gcdavidq/Project_FdD/FdD/Entregables/2.-Definción_del_problema.md

# 2. DEFINICIÓN DEL PROBLEMA:

### **"La cultura ambiental ineficiente respecto a la clasificación de los residuos sólidos domiciliarios en San Martín de Porres, Lima."**

HERRAMIENTAS A UTILIZAR PARA DEFINIR EL PROBLEMA
1.PREGUNTAS AL USUARIO 
Se envió un formulario a los usuarios donde contiene preguntas acerca de la organización de los residuos sólidos. Ellos podrán responder y de esa manera nos daremos cuenta qué tanto conocen acerca del tema o qué tan satisfechos se encuentran con la organización de estos residuos.

1. ¿Qué opina usted acerca de la contaminación ambiental? ¿Cree usted qué el ministerio de ambiente está realizando un buen trabajo?

2. ¿Usted separa los residuos sólidos en su hogar por orgánicos (cáscaras de verduras o frutas) e inorgánicos (papel, aluminio, vidrio etc)? En caso negativo, sí cobran alguna penalidad monetaria por no hacerlo, ¿Usted lo haría?

3. ¿Usted puede diferenciar qué residuos debe ir en cada color de tacho?
4. Si existiera una recolección separada (orgánicos e inorgánicos), ¿usted se motivaría a reciclar?  O si ya recicla, ¿lo haría con mayor gusto?

5. Si los tachos de basura tuvieran una forma relacionada a lo que se debe depositar en él ¿Cree usted que resultaría más fácil clasificar los residuos? Ejemplo: Botella gigante para reciclar plásticos.

6. Si existieran incentivos económicos en el manejo del reciclaje, el manejo de los residuos sólidos, ¿mejoraría o empeoraría? 

7. ¿Qué estrategias considera usted que deben ser usadas para que en nuestro país haya un programa de reciclaje efectivo?

**Enlace de la encuesta:** https://forms.gle/2g3sSfPMJ8BGpuau7

**Evidencias de la encuesta realizada:** https://docs.google.com/spreadsheets/d/1U6mOmiROQCDAYu15ibwH8KvVmI2ISACFjVF0aS-_oU8/edit?usp=sharing

  ***Figura 1:*** Resultados gráficos de la encuesta. Elaboración propia.

**2. MAPA DE EMPATÍA**

El mapa de empatía es una herramienta visual que ayuda a comprender las necesidades, pensamientos, emociones y comportamientos de un usuario(1). Las respuestas de Google Forms nos ayudarán para una buena organización de este mapa.

<p align= "center">
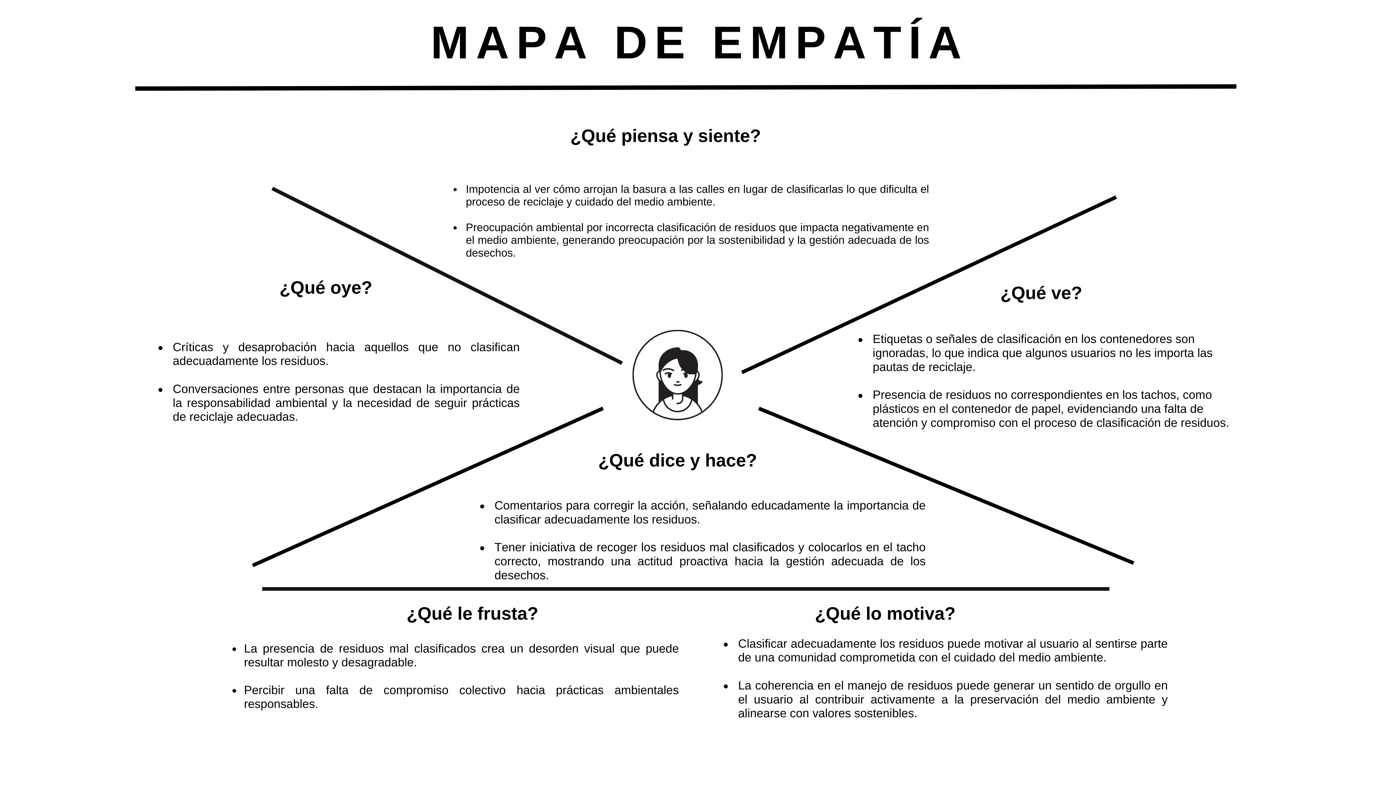
[picture p170: Carpetas_del_Proyecto/Imagenes/C-Definción del problema/b2.-Mapa de empatia.png]
imagen del grupo
  
</p>

***Figura 2:*** Mapa de empatía. Elaboración propia.

3. **DIAGRAMA DE ISHIKAWA:** También conocido como diagrama de causa-efecto, es una herramienta gráfica que identifica y organiza las posibles causas del problema en específico (2).

<p align= "center">
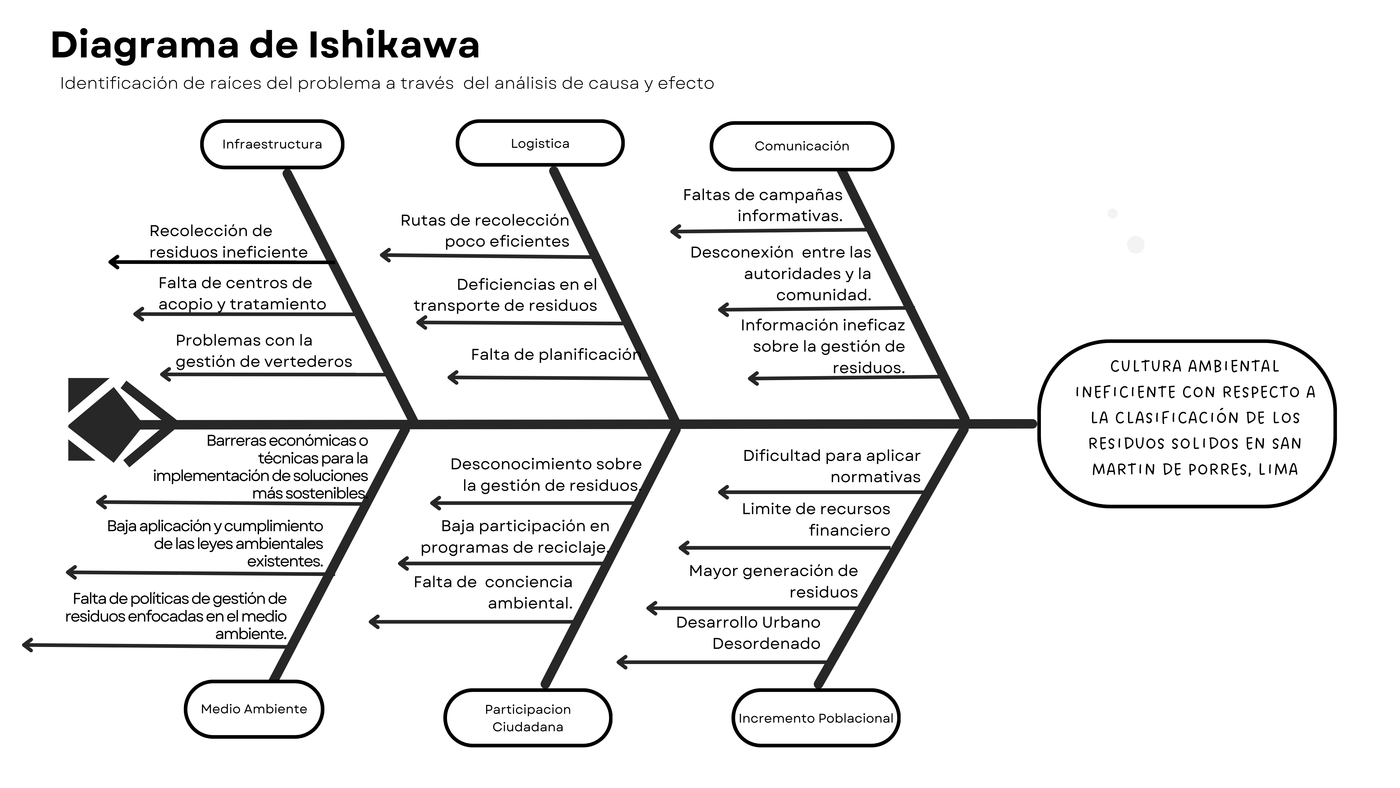
[picture p171: Carpetas_del_Proyecto/Imagenes/C-Definción del problema/c3.-Diagrama de ishikawa.png]
imagen del grupo
  
</p>

   ***Figura 3:***  Diagrama de Ishikawa, Elaboración propia.

4. ***MAPA DE VIAJE DEL PROBLEMA IDENTIFICADO:*** 
Por último, se realizó el Journey Map, este nos permitió conocer el comportamiento del usuario, la situación que vive antes, durante y después de la problemática.

<p align= "center">
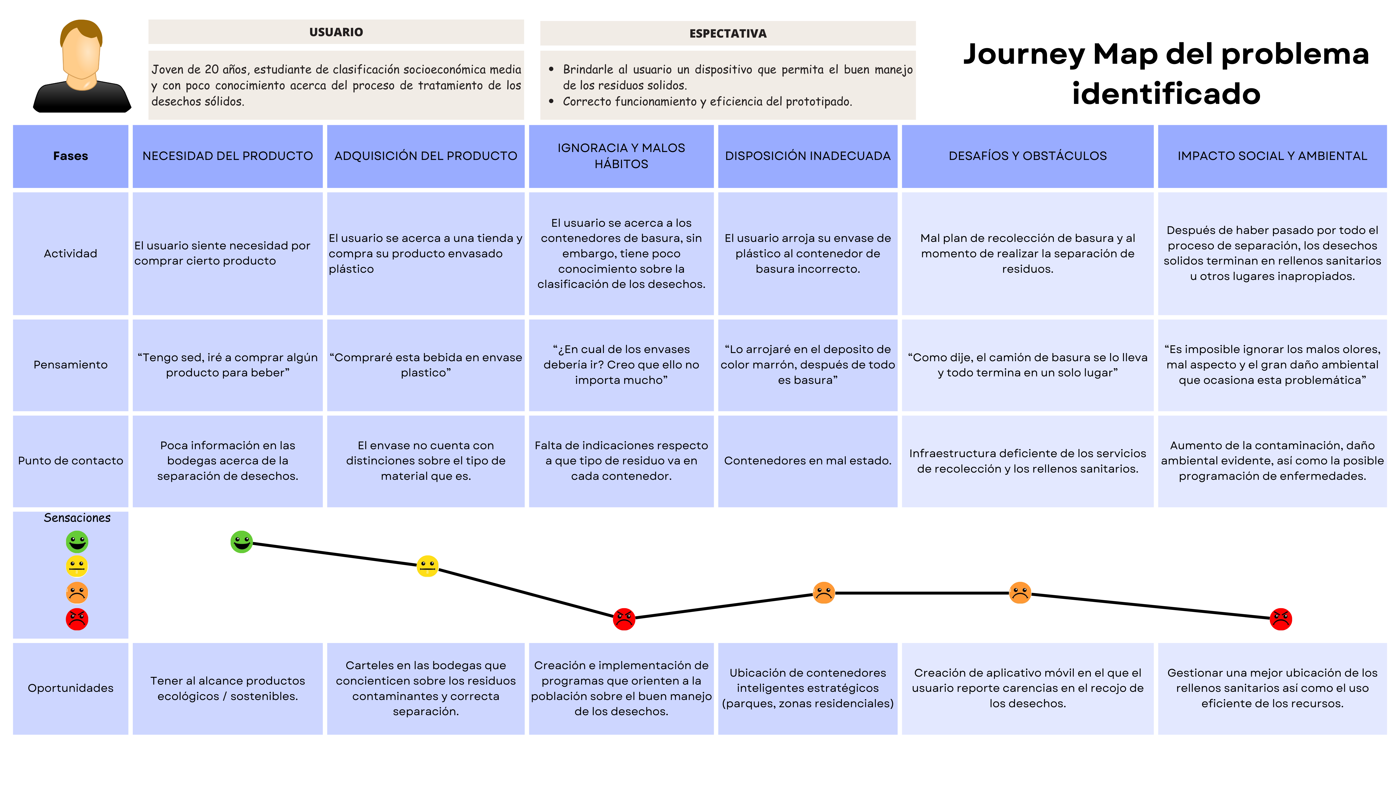
[picture p172: Carpetas_del_Proyecto/Imagenes/C-Definción del problema/d4.-Journey map.png]
imagen del grupo
  
</p>

***Figura 4:***  Journey Map.  Elaboración propia.

5. **DESCRIPCIÓN DE LA PROBLEMÁTICA:**

En la actualidad, la contaminación ambiental se ha convertido en uno de los problemas más críticos y graves a nivel mundial, razón por la cual es sumamente necesario tomar conciencia acerca de ello y buscar alternativas de solución que nos permitan mitigar el problema [3]. La polución está destruyendo la vida de la flora y fauna. Con el pasar de los días se incrementa su proporción en nuestro planeta, siendo nosotros los mayores causantes de este mal, aun sabiendo que ser el humano el ser más inteligente resulta ser incapaz de cuidar su propio planeta [4].

En el país, la gestión de los residuos sólidos se ha convertido en un asunto preocupante, específicamente en la región Lima, lo que afecta la salud y el bienestar de la población. “En algunos de los distritos, la acumulación de basura es tal que dificulta el tránsito adecuado, e incluso ha llevado a los vecinos a tomar cartas en el asunto quemando los montículos de basura acumulados” [5]. El problema de los residuos o de la basura en general tiene varias aristas, pues, por un lado, las autoridades están haciendo una mala gestión, tanto de recolección de residuos y la separación de estos; por otro lado, la falta de educación cívica de los ciudadanos fomenta la acumulación de la basura en los espacios públicos [5].
Hoy en día, el distrito de San Martín de Porres enfrenta una gran cantidad de desperdicio debido a los malos hábitos de los residentes de la zona, que se están extendiendo y causando una gran contaminación ambiental. Necesitamos saber si la gestión adecuada es un método efectivo para evitar la acumulación de desechos con el único propósito de satisfacer las necesidades de los habitantes de manera objetiva y racional sin causar daño a las generaciones futuras [6]. 

<p align= "center">
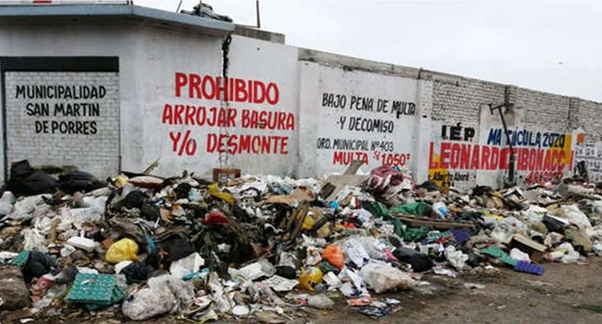
[picture p173: Carpetas_del_Proyecto/Imagenes/C-Definción del problema/e5.-Contexto del problema.png]
imagen del grupo
  
</p>

  ***Figura 5:*** Residuos sólidos depositados en la calle Pastor Bravo y el jirón Gregorio VII, cerca al mercado Megacentro Caquetá. Fue extraído de "Vecinos de SMP hartos de la acumulación de basura" y tomada por Giampier Cerrón Arica(7).

<p align= "center">
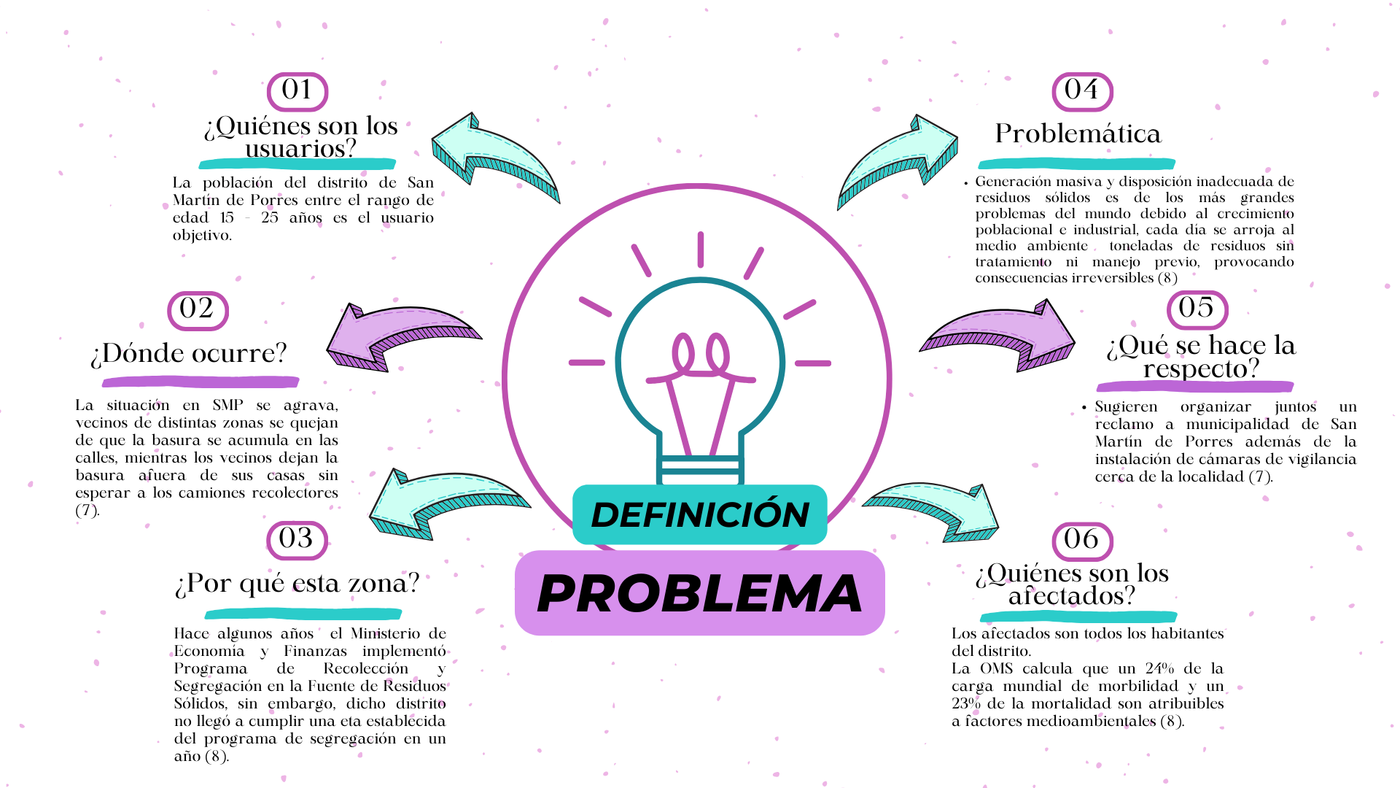
[picture p174: Carpetas_del_Proyecto/Imagenes/C-Definción del problema/f6.-Definición del problema.png]
imagen del grupo
  
</p>

  ***Figura 6:*** Definición del problema. Elaboración propia

**Contexto actual:**
La situación qué se vive en san Martín de Porres es muy preocupante, es por ello qué para dar una mejor evidencia sobre la problemática qué estamos presentando es un hecho y se aprecia día a día en este distrito, recopilamos algunas fotografías en dos puntos específicos uno es el parque Andrés Hurtado y el otro punto es la universidad Peruana Cayetano Heredia.
**Situación del parque Andres Hurtado:**
  -Parque en mal estado
  -Puntos de concentración de desechos 
  -Arrojo de bolsas de basura 
  -Falta de depósitos de basura (en todo el parque no existe ningún tacho de basura).

<p align= "center">
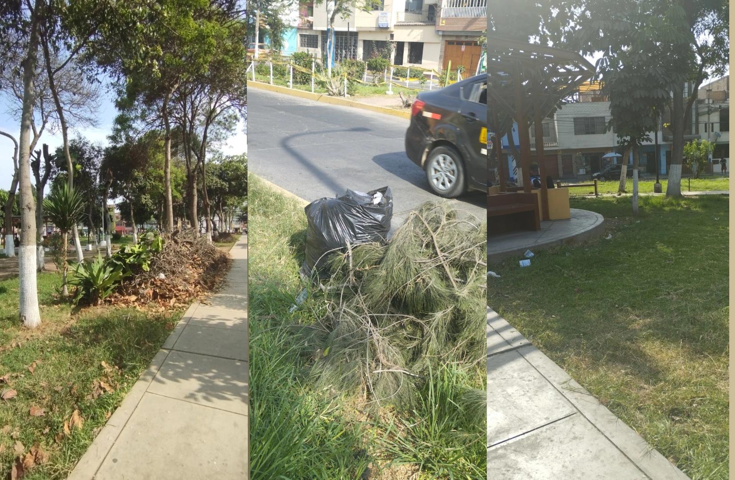
[picture p175: Carpetas_del_Proyecto/Imagenes/C-Definción del problema/g7.-Contexto actual.jpg]
imagen del grupo
  
</p>

***Figura 7:*** Desmonte y basura botada en el  parque Alberto Hurtado ubicado en SMP. Elaboración propia.

<p align= "center">
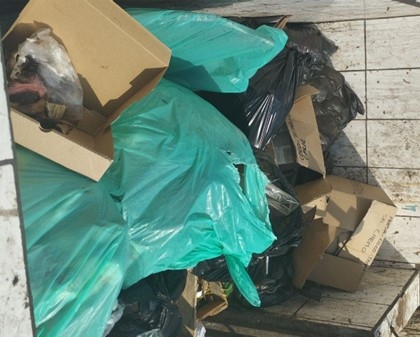
[picture p176: Carpetas_del_Proyecto/Imagenes/C-Definción del problema/g71.-Contexto actual.jpg]
imagen del grupo
  
</p>

***Figura 8:*** Almacenamiento de residuos sólidos frente a UPCH. Elaboración propia.

**Situación del “Botadero frente a la UPCH”:**
  -Recolectores de plástico sacan algunos desechos de este. 
  -Emite olores desagradables para la población.
  -Posiblemente sea un foco de contagio para enfermedades infecciosas.
  -Genera un mal aspecto a la vía pública.

<div style="display: flex; justify-content: space-between;">
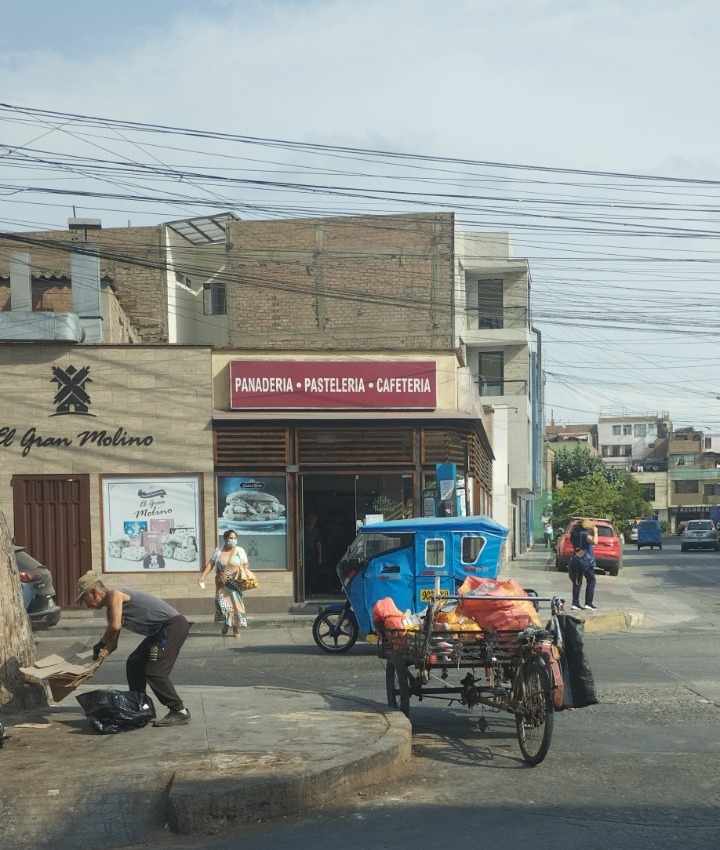
[picture p177: Carpetas_del_Proyecto/Imagenes/C-Definción del problema/h8.-Botadero Frenta a la Upch.jpg]
  
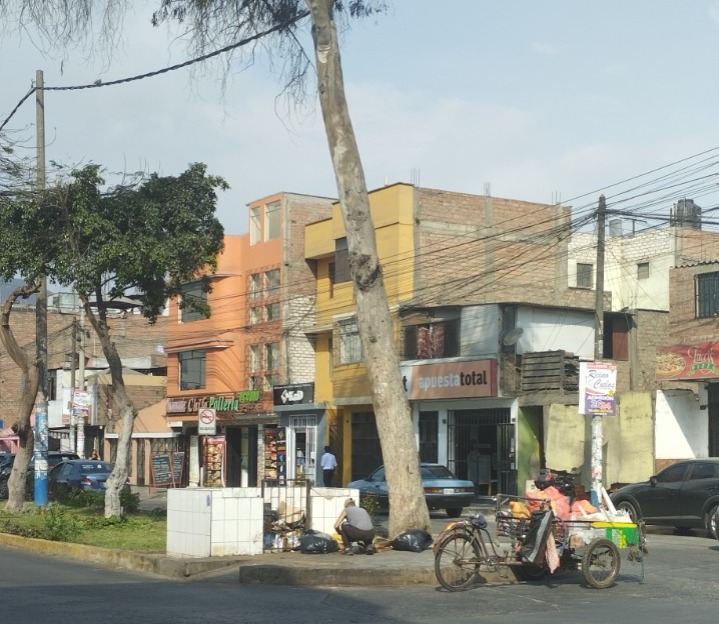
[picture p178: Carpetas_del_Proyecto/Imagenes/C-Definción del problema/h81.-Botadero Frenta a la Upch.jpg]
  
</div>

***Figura 9:***  Recolector informal de residuos sólidos frente a UPCH. Elaboración propia.

**Situación de la UPCH:**
  -Incorrecto uso de los depósitos de basura por parte de los universitarios, profesores y todo el personal administrativo.
  -Falta de contenedores en puntos estratégicos. 
  -Depósitos de desechos innecesarios. 

<p align= "center">
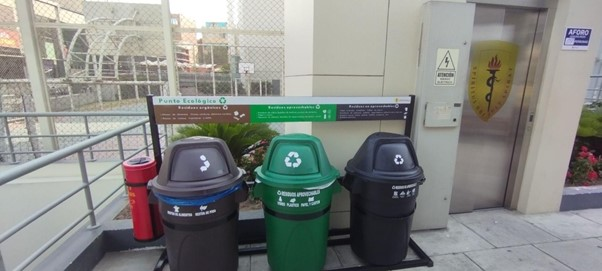
[picture p179: Carpetas_del_Proyecto/Imagenes/C-Definción del problema/i9.-Contexto Upch.jpg]
imagen del grupo
  
</p>

***Figura 10:***  Contenedores de residuos sólidos en UPCH. Elaboración propia.

<p align= "center">
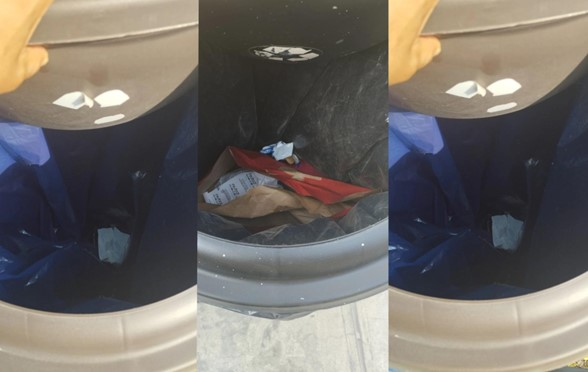
[picture p180: Carpetas_del_Proyecto/Imagenes/C-Definción del problema/i91.-Contexto Upch.jpg]
imagen del grupo
  
</p>

***Figura 11:*** Mala disposición de residuos sólidos en los contenedores de la UPCH. Elaboración propia.

<p align= "center">
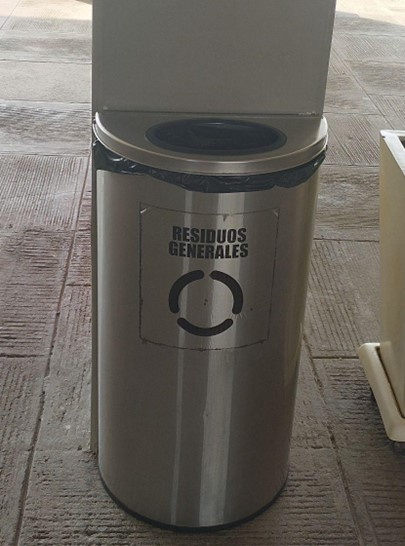
[picture p181: Carpetas_del_Proyecto/Imagenes/C-Definción del problema/i92.-Contexto Upch.jpg]
imagen del grupo
  
</p>

***Figura 12:*** Contenedor de residuos generales en la UPCH. Elaboración propia.

### PROPUESTA DE SOLUCIÓN

Como equipo, hemos estado en constante comunicación y debate de cómo podríamos solucionar esta problemática.  Al inicio nuestra idea fue crear diseños o prototipos de contenedores que tuviese la forma del material que será arrojado en su interior, por ejemplo, que el contenedor en donde se va a depositar los materiales plásticos tenga la forma de una botella, pero la solución era muy primitiva aún, por lo que entonces ideamos incluir la IoT, es por ello que decidimos agregar a nuestra idea inicial que los contendores puedan interactuar con el individuo, y poder identificar residuos, para que cuando incumple con las restricciones suene una alarma y de esa manera las personas aprendan a gestionar sus residuos de la forma adecuada, además de ello nos gustaría que se determine la cantidad de residuos que puede almacenar en su totalidad y así obtener mayor información, por ejemplo, contabilizar la cantidad de botellas que se depositan, las cuales posteriormente podrían ser reutilizables.

<p align= "center">
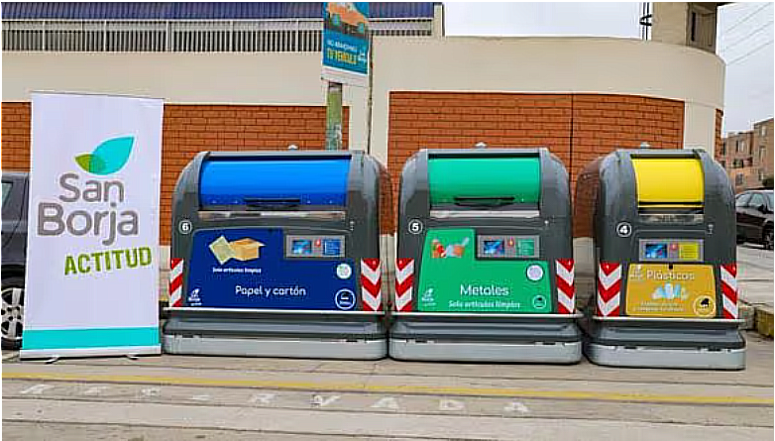
[picture p182: Carpetas_del_Proyecto/Imagenes/C-Definción del problema/k11.-Propuesta solución.png]
imagen del grupo
  
</p>

***Figura 13:*** Contenedores ecológicos ubicados en el distrito de San Borja. Fue extraído de "San Borja: ‘instalan islas ecológicas’ inteligentes para fomentar el reciclaje entre los vecinos"(8).

### BIBLIOGRAFÍA:

1. Pursell S. Qué es un mapa de empatía, cómo crearlo y ejemplos [Internet]. [citado 17 de enero de 2024]. Disponible en: https://blog.hubspot.es/service/mapa-empatia

2. Rodriguez J. Qué es el diagrama de Ishikawa, para qué sirve, cómo crearlo y ejemplos [Internet]. [citado 17 de enero de 2024]. Disponible en: https://blog.hubspot.es/sales/diagrama-ishikawa

3. Palacios Anzules Í, Moreno Castro DW. Contaminación ambiental. RECIMUNDO Rev Científica Investig El Conoc. 2022;6(2):93-103. Disponible en:  https://dialnet.unirioja.es/servlet/articulo?codigo=8374646

4. Perez Quispe Y. LA CONTAMINACIÓN AMBIENTAL. 7 de diciembre de 2021;Disponible en: https://www.researchgate.net/publication/356841723_LA_CONTAMINACION_AMBIENTAL

5. Vela-Anda D. ANÁLISIS DE SOLUCIONES PARA LA ACUMULACIÓN DE BASURA EN LIMA METROPOLITANA Y CALLAO. Disponible en: https://pirhua.udep.edu.pe/backend/api/core/bitstreams/b0d37225-43b9-4709-8b55-d025768fff43/content

6. Aguilar DSF, Carlos J, Arenaza DD, Demetrio V. TESIS PARA OBTENER EL TÍTULO PROFESIONAL DE: Licenciado en Administración.Disponible en: https://repositorio.ucv.edu.pe/bitstream/handle/20.500.12692/53351/De%20Souza_FAJC-SD.pdf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

7. Escolares C. Vecinos de SMP hartos de la acumulación de basura. El Comercio [Internet]. 15 de agosto de 2022 [citado 17 de enero de 2024]; Disponible en: https://elcomercio.pe/corresponsales-escolares/historias/vecinos-de-smp-hartos-de-la-acumulacion-de-basura-san-martin-de-porres-contaminacion-basura-noticia/ 

8. Redacción EC. San Borja: ‘instalan islas ecológicas’ inteligentes para fomentar el reciclaje entre los vecinos. El Comercio [Internet]. 21 de julio de 2022 [citado 18 de enero de 2024]; Disponible en: https://elcomercio.pe/lima/sucesos/san-borja-instalan-islas-ecologicas-inteligentes-para-fomentar-el-reciclaje-entre-los-vecinos-rmmn-noticia/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
