gcdavidq/Project_FdD/FdD/Entregables/1.-Sobre_Nosotros.md

# 1. NOSOTROS

### Objetivo del presente archivo: 

En este apartado se encontrarán aspectos importantes para que nos puedan conocer a cada uno de los integrantes, como por ejemplo nuestras carreras o intereses personales. Más allá de ello, también nos conocerán como grupo. Esto implica saber quiénes somos, cuáles son nuestras fortalezas, misión y visión.

## ¿Quienes somos?

Somos un grupo de estudiantes de la Universidad Peruana Cayetano Heredia que tienen el deseo y compromiso de aportar con sus conocimientos y voluntad para mejorar el país y concientizar a la población respecto al consumo responsable.

## Nuestra Misión: 
Generar un prototipo que ayude y permita a la sociedad peruana a tener un consumo responsable y de esa manera incentivar a una mejor cultura ambiental.

## Nuestra Visión:
Convertirnos en un grupo de estudiantes universitarios que contribuyan en su país a reducir el impacto de la mala distribución y aprovechamiento de los residuos sólidos domiciliarios por medio del prototipo creado e implementado.

## Conociendonos un poco más: 

A continuación, se brindará algunas caracteristicas de cada integrante del grupo.

### Herrera Jhunior - (jhunior.herrera@upch.pe)

**Carrera:** Ing Informática

**Edad:** 19

**Breve Descripción:** 

Estudiante de la carrera de Ingeniería Informática interesado en mejoras e innovación para las tecnologías del Perú y el mundo, así mismo apoyar a las comunidades y entornos de necesidad con nuevas herramientas para su sostenibilidad, también le gustaría participar en proyectos de prótesis robóticas y todo el entorno de mejoras para el ser humano y sus capacidades, es una persona perseverante, entusiasta y le gustaría ayudar a este mundo a ser un poco mejor, también tiene un canal de YouTube donde subo todo tipo de contenido.

**Rol que desempeñará:** 

*"Coordinador de electronica y manufuctura"*: Encargado del hardware, manipulación y gestión de los materiales que se utilizarán durante este proyecto, director de pruebas y control de calidad que proporcionen mejores habilidades para diseñar y mejorar con base de prueba y error, de esa manera ofrecer una garantía plena, encargado del mantenimiento y resolución de problemas, así como de seguridad para el equipo.

**Imagen Referencial**

<p align= "center">
  imagen del grupo
</p>

### Quezada Marceliano Gian Carlos - (gian.quezada@upch.pe)

**Carrera:** Ing Informática

**Edad:** 18

**Breve Descripción:** 

Estudiante de la carrera de Ingeniería Informática interesado en un enfoque en el área de Ciberseguridad y Ciencia de Datos. Tiene como principal propósito ayudar y mejorar los sistemas y programas que ofrecen tanto empresas públicas como privadas con el fin de evitar que sean vulnerables. Entre las habilidades que destaca están el trabajo en equipo, ser social y ser capaz de brindar solución a todo tipo de dificultades que se nos presente. Me gusta leer, escuchar música y practicar deporte.

**Rol que desempeñará:**

*"Coordinador del área de programación y de la página web"*: Encargado de implementar el lenguaje de programación Python en las diversas áreas de nuestro proyecto, así como también crear, diseñar, distribuir, organizar y editar la página web.

**Imagen Referencial**

<p align= "center">
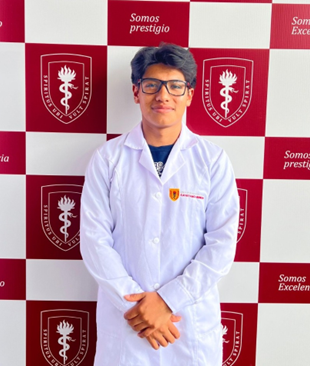
[picture p183: Carpetas_del_Proyecto/Imagenes/B-Participantes_photos/Gian.png]
imagen del grupo
  
</p>

### Ramos Guelac Maximiliana - (maximiliana.ramos@upch.pe)

**Carrera:** Ing Ambiental

**Edad:** 19

**Breve Descripción:** 

Estudiante de la carrera de Ingeniería Ambiental interesada en el rubro de economía ambiental. En su tiempo libre le gusta escuchar música mientras camina, salir con sus amigos y familiares, ama la comida. Se considera como una persona empática, honesta y sobre todo le gusta trabajar en equipo.

**Rol que desempeñará:** 

*"Coordinadora del área de selección de materiales"*: Encargada del manejo de inventario, la supervisión de productos y materiales e inspección de los envíos de equipos, así como también del proceso de selección adecuada de los mismos.

**Imagen Referencial**

<p align= "center">
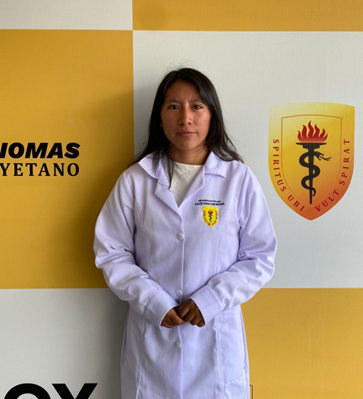
[picture p184: Carpetas_del_Proyecto/Imagenes/B-Participantes_photos/Maxi.png]
imagen del grupo
  
</p>

### Vazques Nuñez Maylin - (america.vasquez@upch.pe)

**Carrera:** Ing Ambiental

**Edad:** 19

**Breve Descripción:** 

Estudiante de la carrera de Ingeniería Ambiental interesada en el rubro de restauración y cuidado de las áreas naturales. En su tiempo libre le gusta jugar vóley con sus amigos y familiares, le encanta bailar y escuchar música, también se considera una persona amigable, empática, alegre y sobre todo le gusta trabajar en equipo.

**Rol que desempeñará:** 

*"Coordinadora del área de redacción y prototipado"*: Encargada del diseño y la elaboración de moldes para la construcción de prototipos, asimismo, de verificar que el texto escrito sea coherente y conciso.

**Imagen Referencial**
<p align= "center">
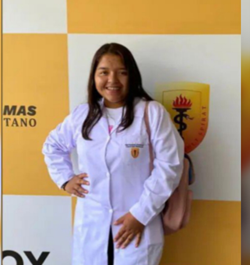
[picture p185: Carpetas_del_Proyecto/Imagenes/B-Participantes_photos/Maylin.png]
imagen del grupo
  
</p>

### Villareal Zapata Liz - (liz.villarreal@upch.pe)

**Carrera:** Ing Ambiental

**Edad:** 18

**Breve Descripción:** 

Estudiante de la carrera de Ingeniería Ambiental, interesada en el rubro de la conservación y restauración de la flora y fauna del Perú y sus alrededores. En sus tiempos libres le gusta escuchar música, leer y/o pintar, en especial le gusta pintar paisajes y atardeceres. Asimismo, le encanta estar en contacto con la naturaleza y caminar por el parque. Se considera una persona amigable y solidaria con los demás.

**Rol que desempeñará:**

*"Coordinadora de la investigación y gestora del proyecto"*:  Encargada de planificar las actividades por desarrollar dentro del equipo de trabajo y verificar que las fuentes de información e investigación sean de calidad y alta validación con el fin de fomentar el trabajo en equipo y el espíritu investigador.

**Imagen Referencial**

<p align= "center">
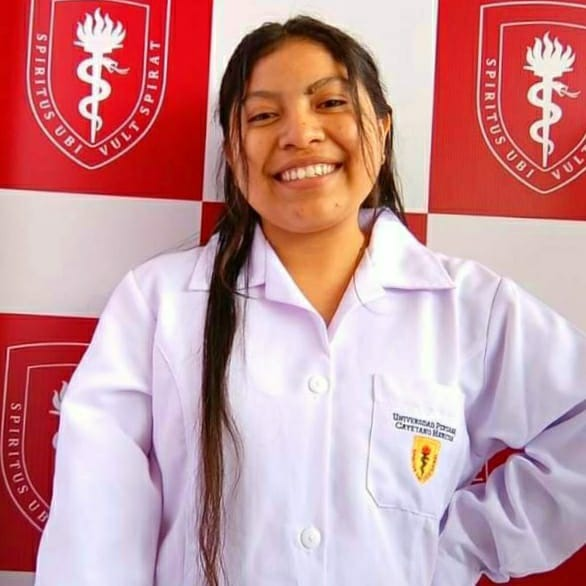
[picture p186: Carpetas_del_Proyecto/Imagenes/B-Participantes_photos/Liz.jpeg]
imagen del grupo
  
</p>
