gcdavidq/Project_FdD/FdD/Entregables/Sobre_Nosotros.md

# NOSOTROS

### Objetivo del presente archivo: 

En este apartado, se encontrarán aspectos importantes para que nos puedan conocer a cada uno de los integrantes, como por ejemplo nuestras carreras o intereses personales. Más alla de ello, tambien nos conoceran como grupo, ello implica sabes quienes somos, cuales son nuestras fortalezas, mision y vision. 

## Conociendonos un poco más: 

A continuación, se brindará algunas caracteristicas de cada integrante del grupo.

### Herrera Jhunior

**Carrera:** Ing. Informatica

**Edad:** 19

**Breve Descripción:** 

Estudiante de la carrera de Ingeniera Informática interesado en mejoras e innovación para las tecnologías del Perú y el mundo, así mismo apoyar a las comunidades y entornos de necesidad con nuevas herramientas para su sostenibilidad, también quiero participar en proyectos de prótesis robóticas y todo el entorno de mejoras para el ser humano para mejorar capacidades, soy perseverante, entusiasta y me gustaría ayudar a este mundo a ser un poco mejor, también tengo un canal de YT donde subo cualquier cosa (datito).

**Rol que desempeñará:** 

*"Coordinador de electronica y manufuctura"*: Encargado del hardware, manipulación y  gestión de la materiales que se utilizaran durante este proyecto, director de prubas y control de calidad que proporcinen mejores hablididades para diseñar y mejorar con base de prueba y error para ofrecer una garantia plena, encargado del mantenimiento y resolución de problemas asi como de seguridad para el equipo.

**Imagen Referencial**

<p align= "center">
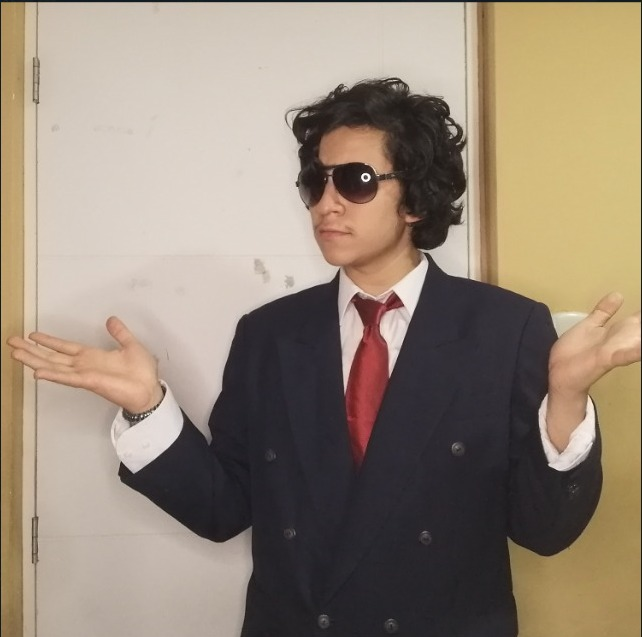
[picture p187: Carpetas_del_Proyecto/Imagenes/Participantes_photos/Jhunior.jpeg]
imagen del grupo
  
</p>

### Quezada Marceliano Gian Carlos

**Carrera:** Ing. Informatica

**Edad:** 18

**Breve Descripción:** 

Estudiante de la carrera de Ingenieria Informatica interesado en un enfoque en el area de Ciberseguridad y ciencia de Datos. Tengo como principal proposito ayudar y mejorar los sistemas y programas que ofrecen tanto empresas publicas y privadas con el fin de evitar que sean vulnerables. Entre las habilidades mias que destaco están el trabajo en equipo, ser social y ser capáz de brindar solucion a todo tipo de dificultades que se nos presente. Me gusta leer, escuchar musica y practicar deporte. 

**Rol que desempeñará:**

*"Coordinador del área de programación y de la página web"*: Encargado de implementar el lenguaje de programación Python en las diversas áreas de nuestro proyecto, así como también crear, diseñar, distribuir, organizar y editar la pagina web

**Imagen Referencial**

<p align= "center">
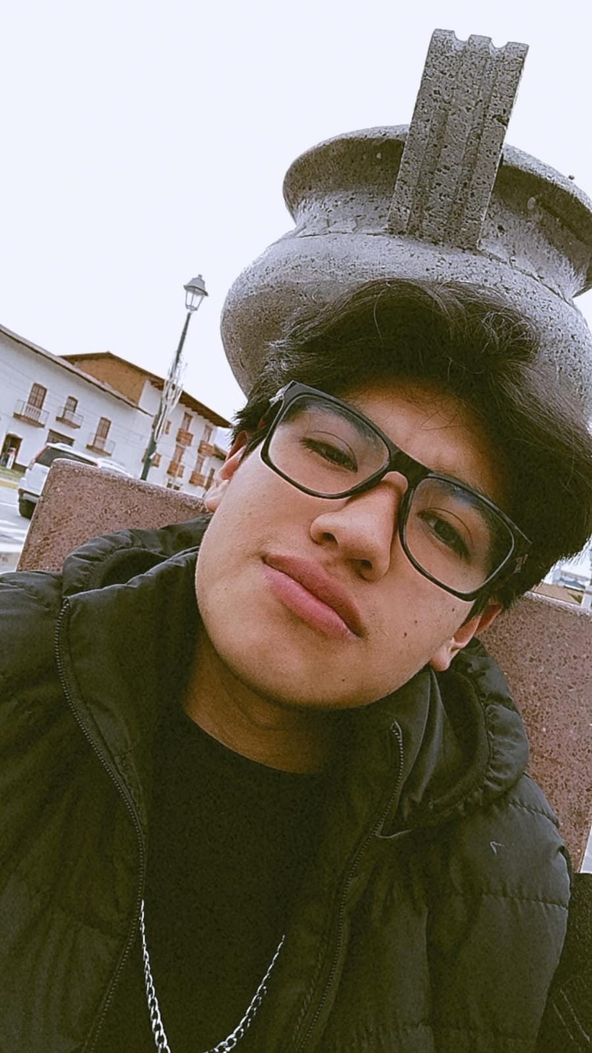
[picture p188: Carpetas_del_Proyecto/Imagenes/Participantes_photos/Gian.jpeg]
imagen del grupo
  
</p>

### Ramos Guelac Maximiliana

**Carrera:** Ing. Ambiental

**Edad:** 19

**Breve Descripción:** 

Estudiante de la carrera de Ingeniería Ambiental  interesada en el rubro de economía ambiental. 
En mi tiempo libre me gusta escuchar música mientras camino, salir con mis amigos y familiares, amo la comida.
Me considero como persona empática, honesta y sobre todo me gusta trabajar en equipo.

**Rol que desempeñará:** 

*"Coordinadora del área de selección de materiales"*: Encargada del manejo de inventario, la supervisión de productos y materiales e inspección de los envíos de equipos así como también del proceso de selección adecuada de los mismos.

**Imagen Referencial**

<p align= "center">
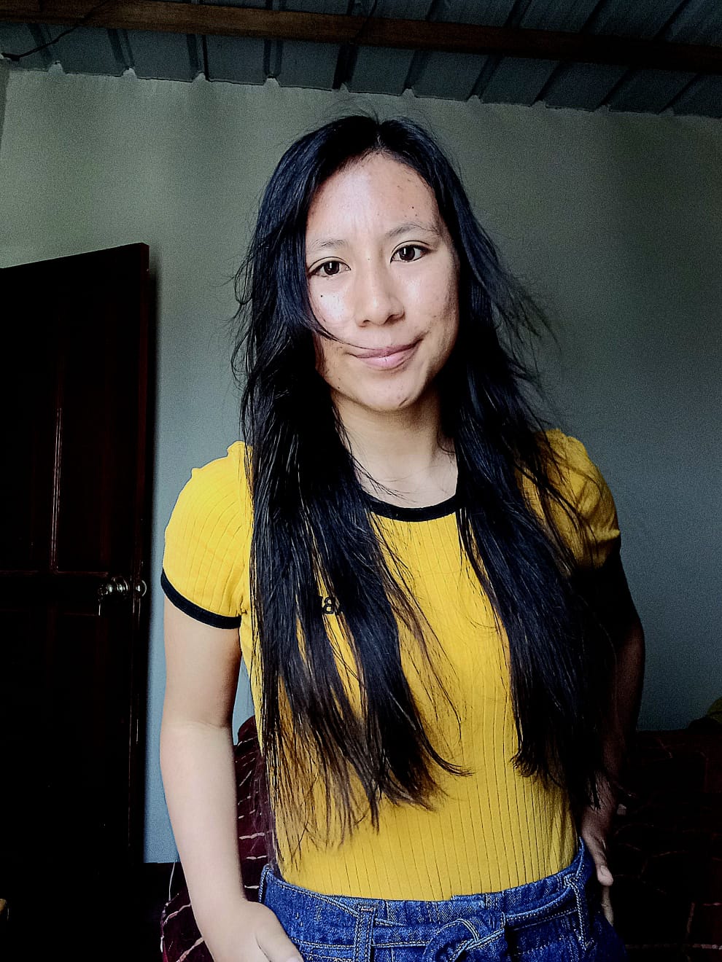
[picture p189: Carpetas_del_Proyecto/Imagenes/Participantes_photos/Maxi.jpeg]
imagen del grupo
  
</p>

### Vazques Nuñez Maylin 

**Carrera:** Ing. Informatica

**Edad:** 19

**Breve Descripción:** 

Estudiante de la carrera de Ingeniería Ambiental  interesada en el rubro de restauración y cuidado de las áreas naturales. En mi tiempo libre me gusta ir a jugar voley con mis amigos y familiares, me encanta bailar y escuchar música también  me considero una persona amigable, empática, alegre y sobre todo me gusta trabajar en equipó.

**Rol que desempeñará:** 

*"Coordinadora del area de redacción y prototipado"*: Encargada del diseño y la elaboración de moldes para la construcción de prototipos. Encargada de verificar que el texto escrito sea coherente y conciso.

**Imagen Referencial**
<p align= "center">
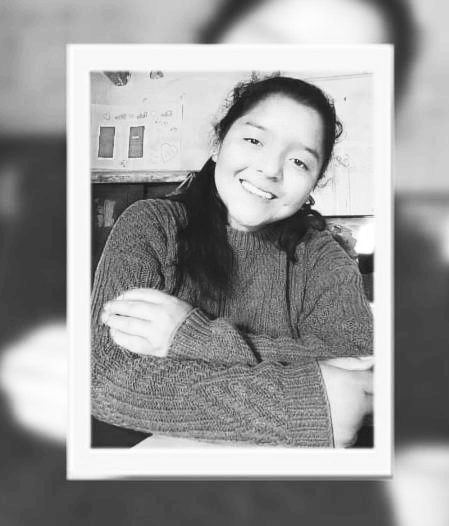
[picture p190: Carpetas_del_Proyecto/Imagenes/Participantes_photos/Maylin.jpeg]
imagen del grupo
  
</p>

### Villareal Zapata Liz

**Carrera:** Ing. Ambiental

**Edad:** 19

**Breve Descripción:** 

Estudiante de la carrera de Ingeniería Ambiental, interesada en el rubro de la conservación y restauración de la flora y fauna de nuestro país y sus alrededores. En mis tiempos libres me gusta escuchar música, leer y/o pintar, en especial me gusta pintar paisajes y atardeceres,  asimismo, me gusta estar en contacto con la naturaleza y caminar por el parque. Me considero una persona amigable y solidaria con los demás.

**Rol que desempeñará:**

*"Coordinadora de la investigación y gestora del proyecto"*:  Encargada de planificar las actividades por desarrollar dentro del equipo de trabajo y verificar que las fuentes de información e investigación sean de calidad y alta validación con el fin de fomentar el trabajo en equipo y el espíritu investigador.

**Imagen Referencial**

<p align= "center">
  imagen del grupo
</p>

## ¿Quienes somos?

Somos un grupo de estudiantes que tienen el deseo de aportar un granito de arena para mejorar el pais y conscientizar a la población respecto al consumo responsable.

## Nuestra Misión: 
Generar un prototipo que ayude y permita a la sociedad Peruana ser responsable en el tema del consumo de alimentos.

## Nuestra Visión:
Disminuir en gran medida el consumo de alimentos que tienen las familias y con ello...!
