gcdavidq/Project_FdD/Carpetas_del_Proyecto/Hardware/1.- Proyectos_preliminares/1.- PROYECTO PRELIMINAR 1.pdf

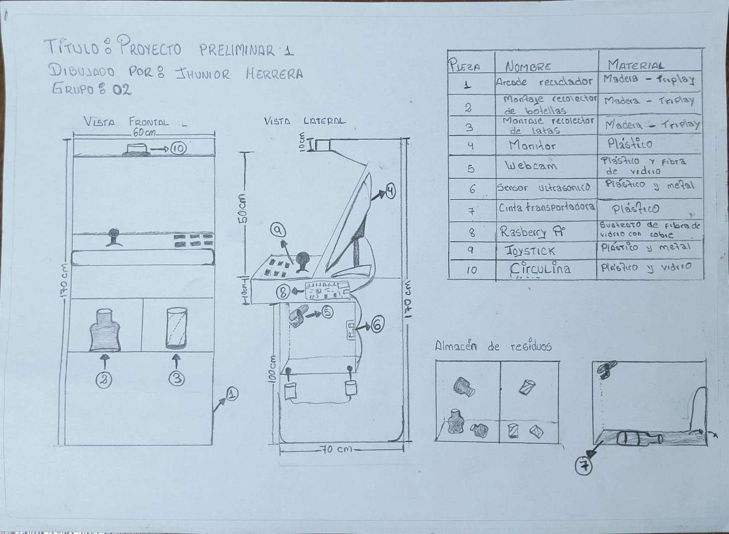
[picture p194: page 1]
