gcdavidq/Project_FdD/Carpetas_del_Proyecto/Hardware/1.- Proyectos_preliminares/2.- PROYECTO PRELIMINAR 2.pdf

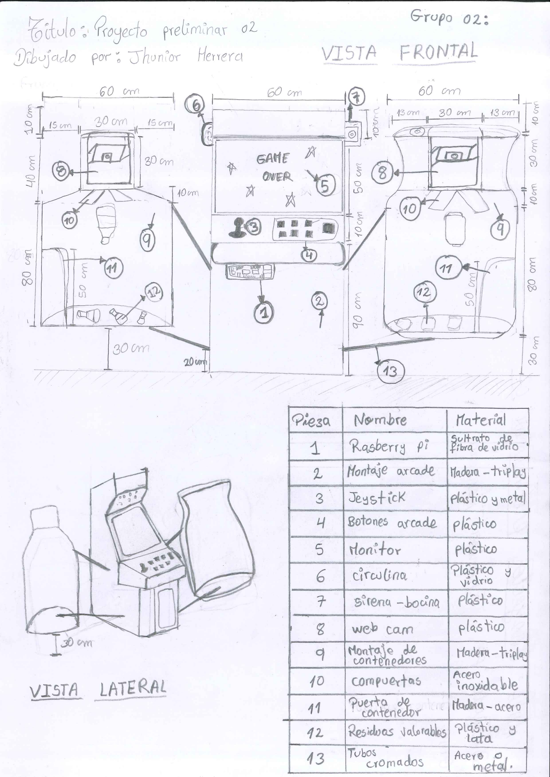
[picture p195: page 1]
