gcdavidq/Project_FdD/Carpetas_del_Proyecto/Hardware/1.- Proyectos_preliminares/3.- PROYECTO PRELIMINAR 3.pdf

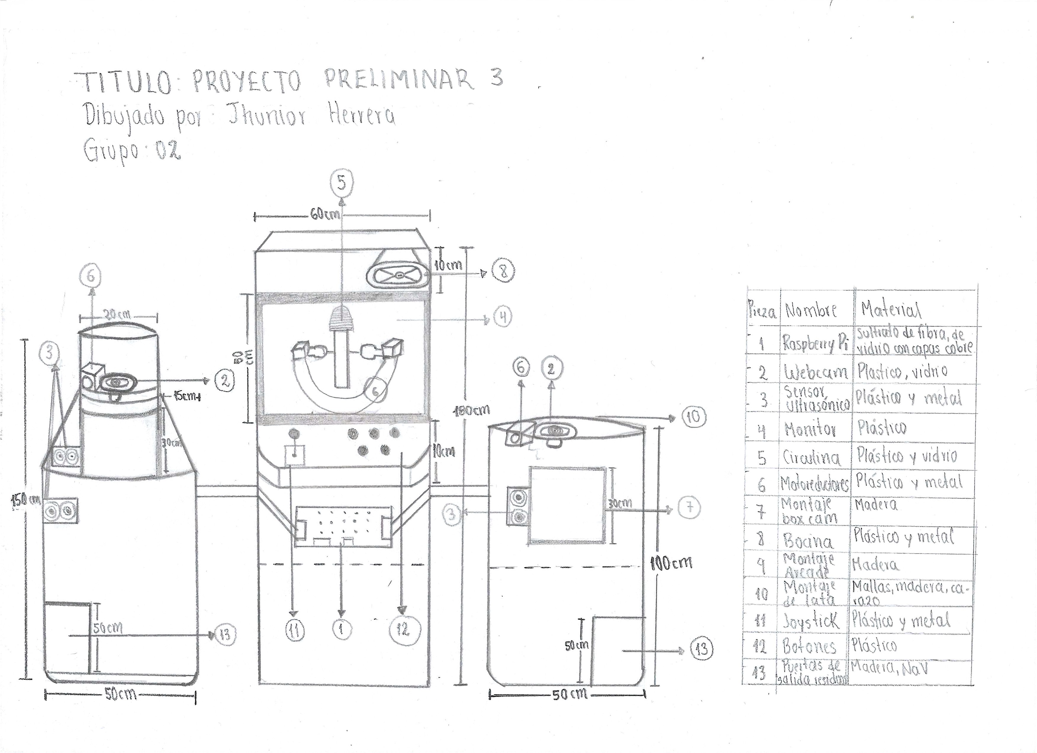
[picture p196: page 1]
