gcdavidq/Project_FdD/Carpetas_del_Proyecto/Imagenes/B-Participantes_photos/Total_group.jpeg

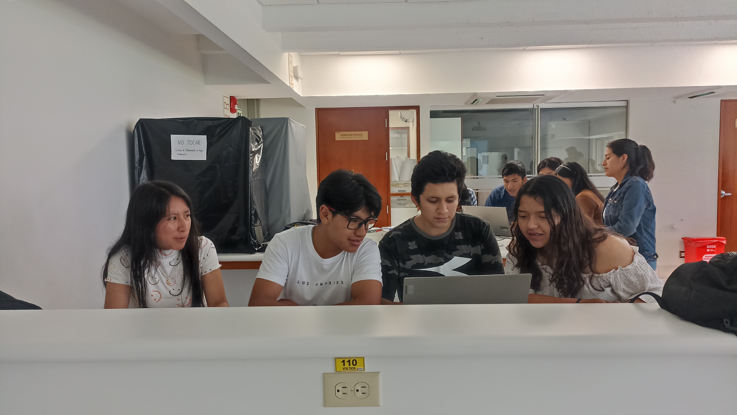
Carpetas_del_Proyecto/Imagenes/B-Participantes_photos/Total_group.jpeg
