gcdavidq/Project_FdD/Carpetas_del_Proyecto/Imagenes/C-Definción del problema/a1.-Encuesta.jpg

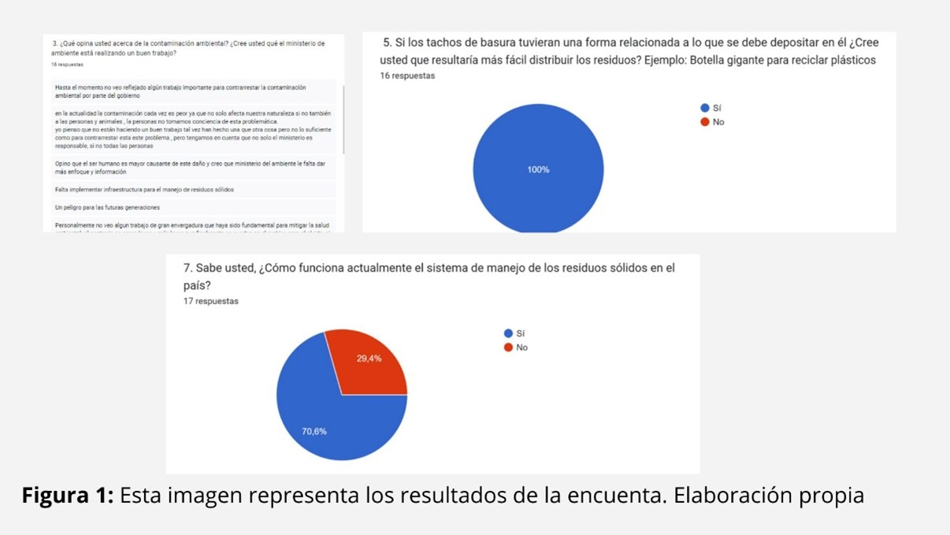
Carpetas_del_Proyecto/Imagenes/C-Definción del problema/a1.-Encuesta.jpg
