gcdavidq/Project_FdD/Carpetas_del_Proyecto/Imagenes/G-Caja negra y funciones/d41.-Funciones.jpg

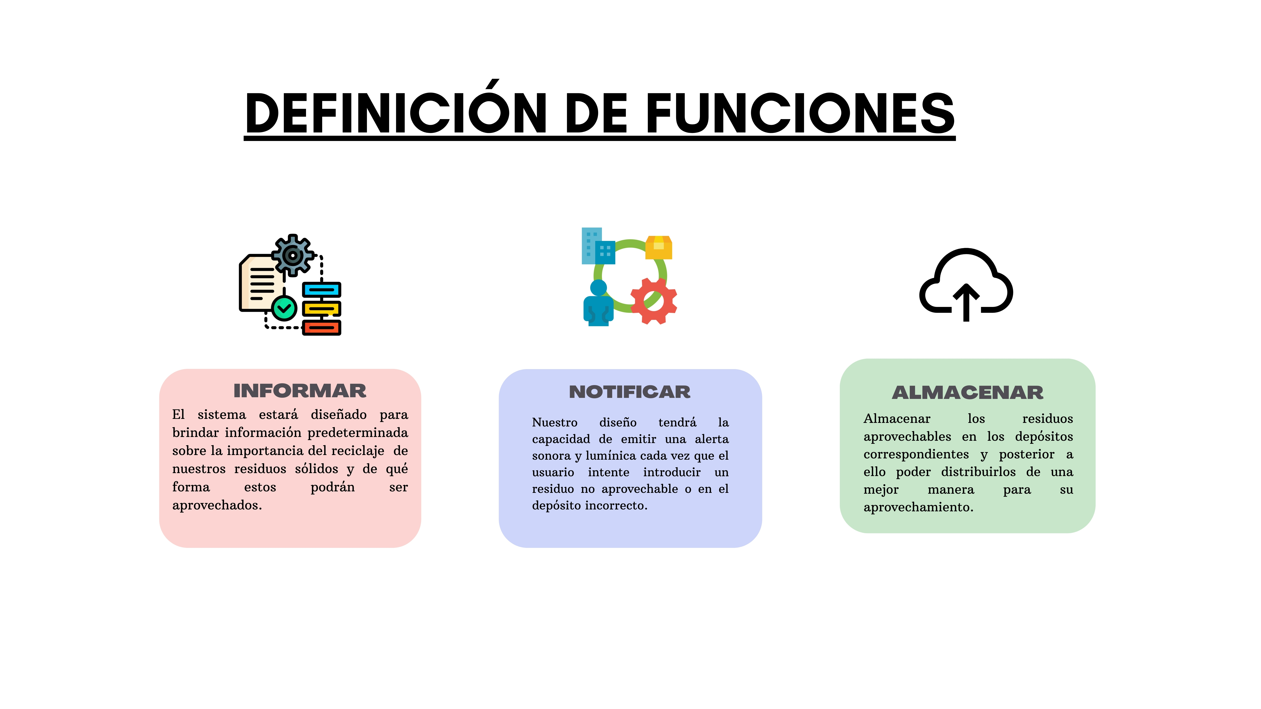
Carpetas_del_Proyecto/Imagenes/G-Caja negra y funciones/d41.-Funciones.jpg
