gcdavidq/Project_FdD/Carpetas_del_Proyecto/Imagenes/Photos_lab/m15.-Grupo trabajando.jpeg

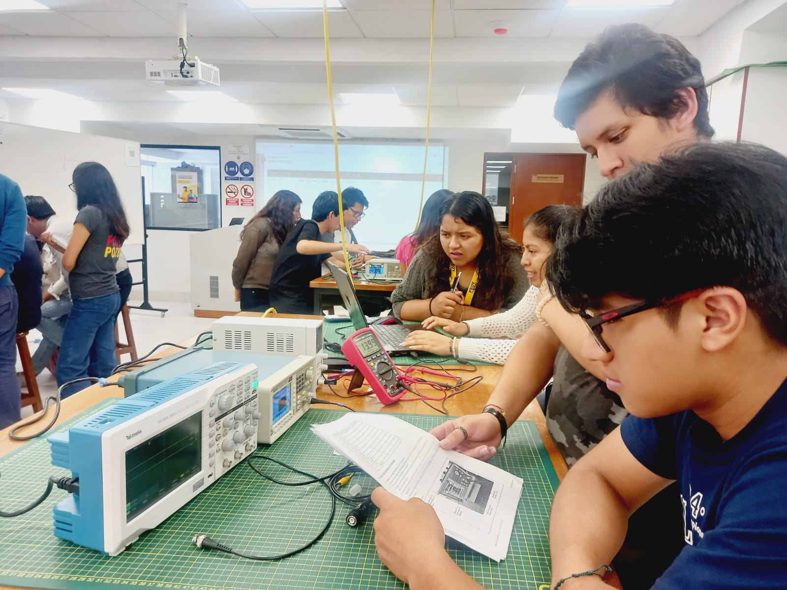
Carpetas_del_Proyecto/Imagenes/Photos_lab/m15.-Grupo trabajando.jpeg
